Wright4TheJob/PiKwonDo/Block Diagram/Block Diagram/Judge Logic.png

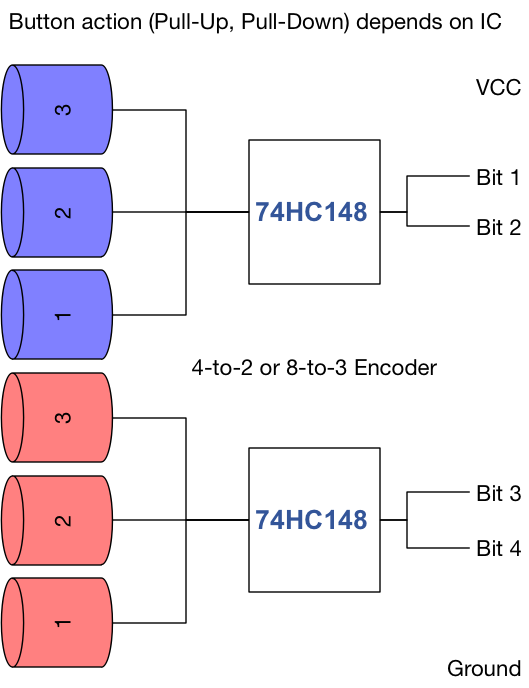
Block Diagram/Block Diagram/Judge Logic.png
