Wright4TheJob/PiKwonDo/Block Diagram/Block Diagram/Software Flow.png

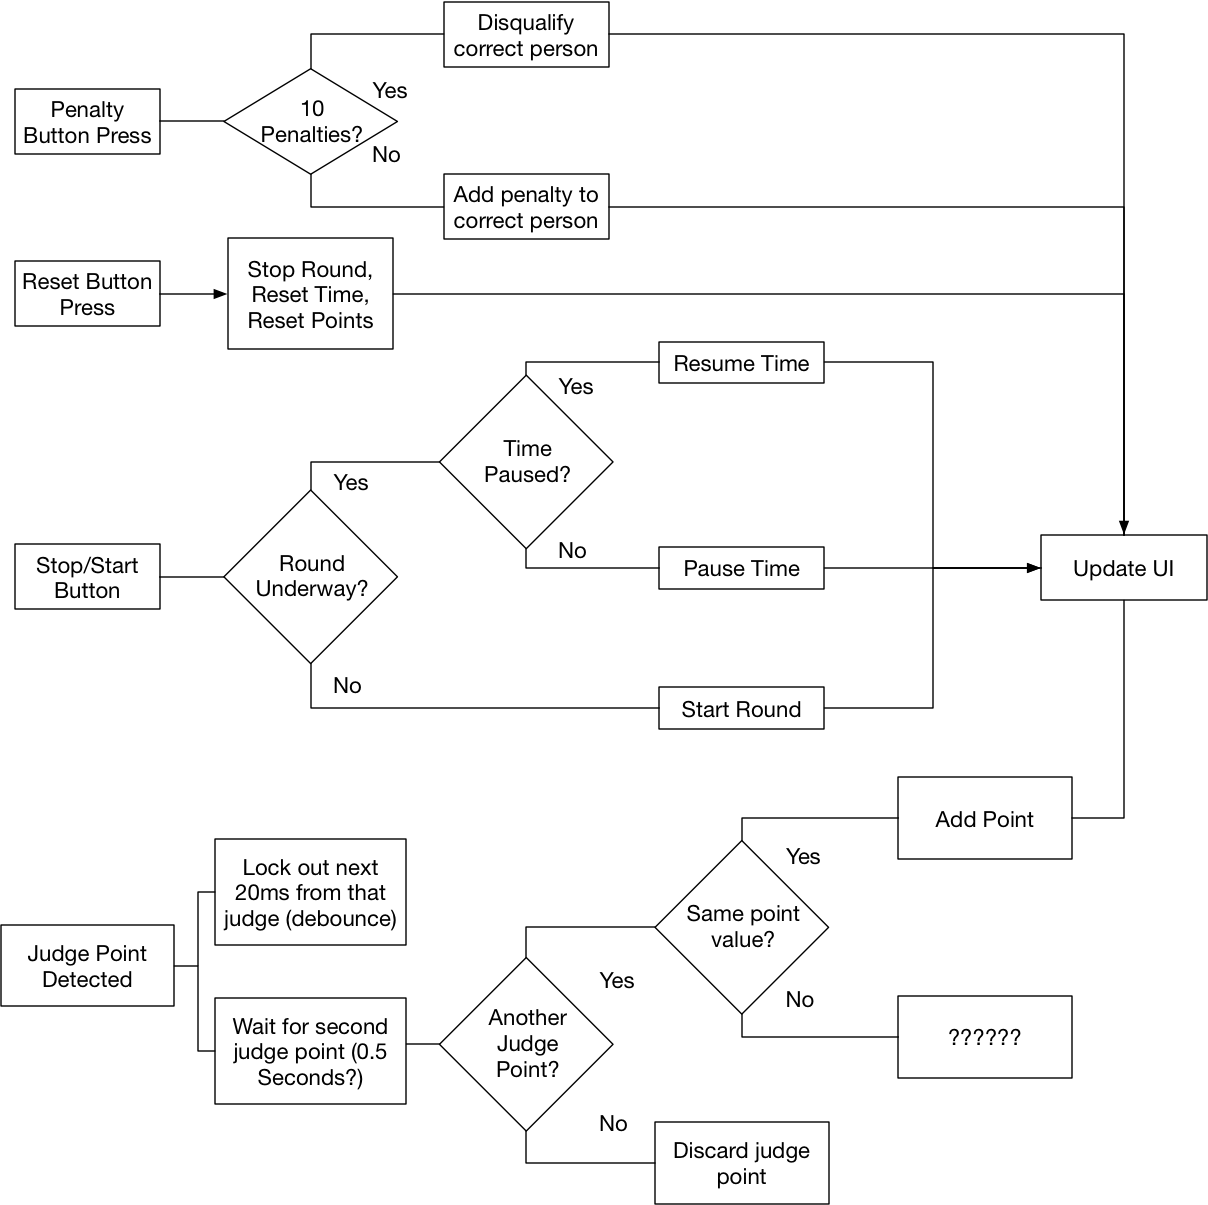
Block Diagram/Block Diagram/Software Flow.png
