Wright4TheJob/PiKwonDo/Block Diagram/Block Diagram/System Diagram.png

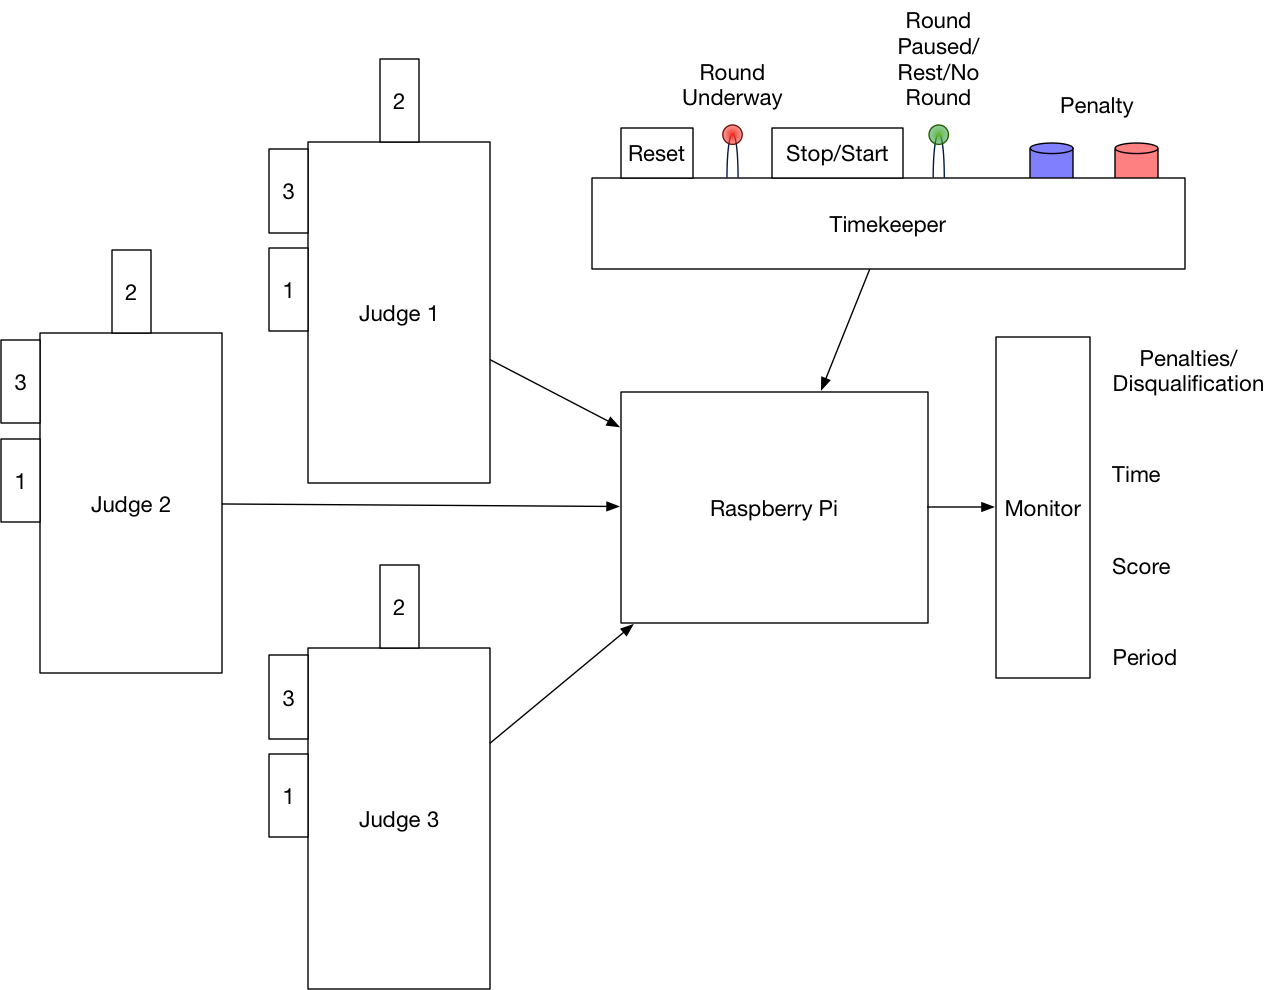
Block Diagram/Block Diagram/System Diagram.png
