Wright4TheJob/PiKwonDo/Hardware/Judge Box/Button Layouts/ButtonGrid.png

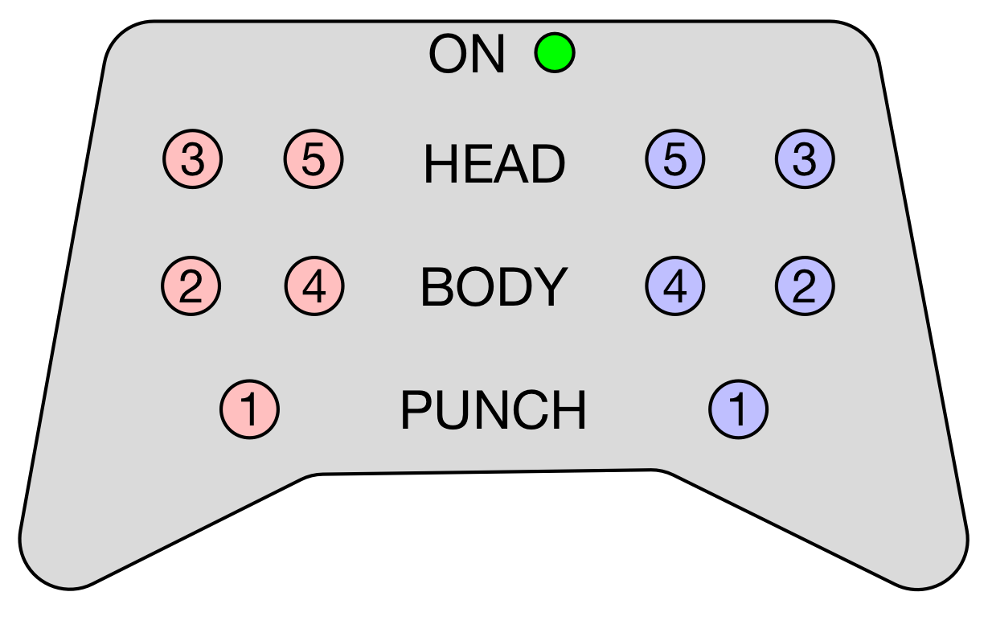
Hardware/Judge Box/Button Layouts/ButtonGrid.png
