Wright4TheJob/PiKwonDo/Hardware/Judge Box/Button Layouts/ButtonLine.png

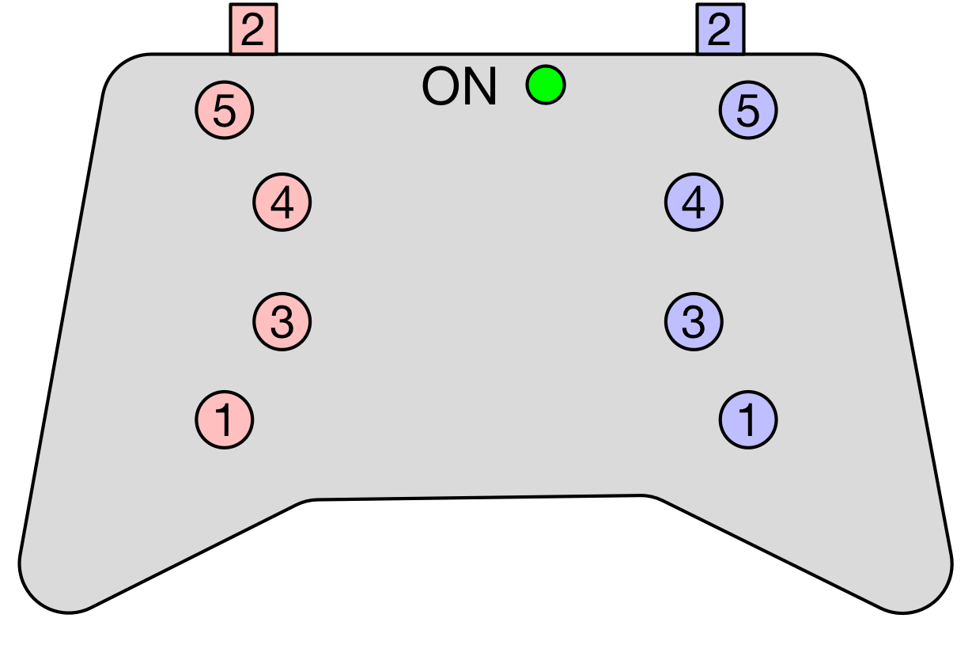
Hardware/Judge Box/Button Layouts/ButtonLine.png
