Wright4TheJob/PiKwonDo/Hardware/Main Box/Raspberry Pi Zero/32,768 Khz Crystal.SLDPRT

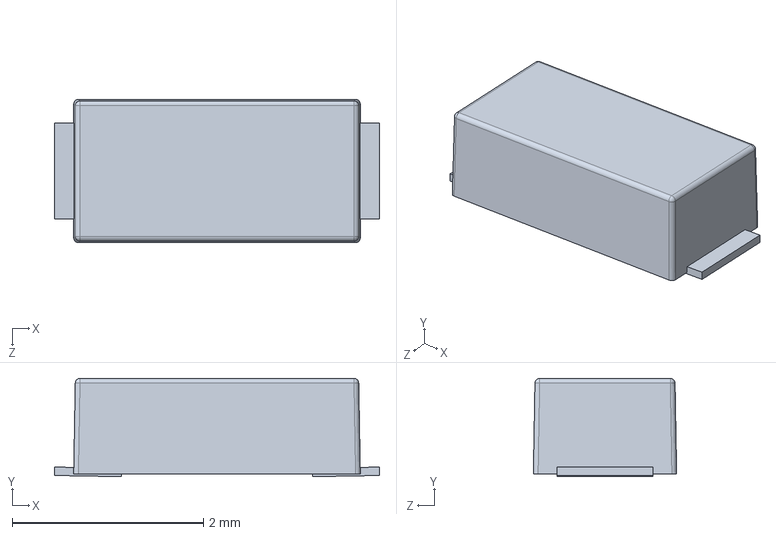
[picture p21: CAD file, 2020-05-05]
Hardware/Main Box/Raspberry Pi Zero/32,768 Khz Crystal.SLDPRT
3.40 x 1.03 x 1.50 mm
