Wright4TheJob/PiKwonDo/Hardware/Common Components/TriggerButton.SLDPRT

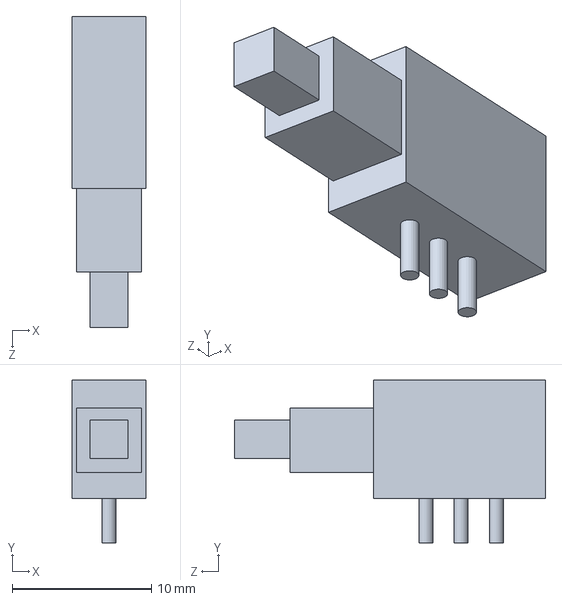
[picture p22: CAD file, 2020-07-26]
Hardware/Common Components/TriggerButton.SLDPRT
5.35 x 11.7 x 22.4 mm
