Wright4TheJob/PiKwonDo/Hardware/Judge Box/JudgeEnclosureBackSolid.3MF

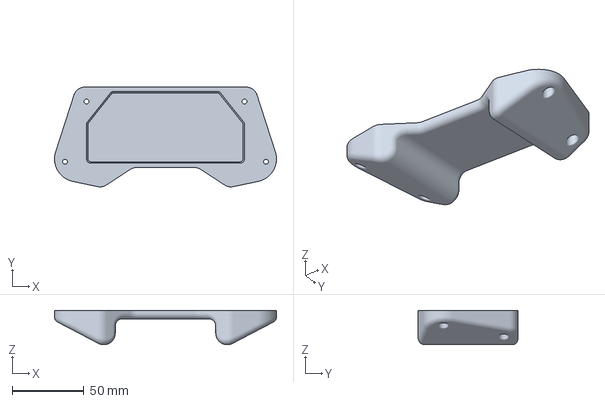
[picture p23: CAD file, 2020-08-09]
Hardware/Judge Box/JudgeEnclosureBackSolid.3MF
154.6 x 69.5 x 24.0 mm
