Wright4TheJob/PiKwonDo/Hardware/Main Box/Raspberry Pi Zero/hdmi type C.SLDPRT

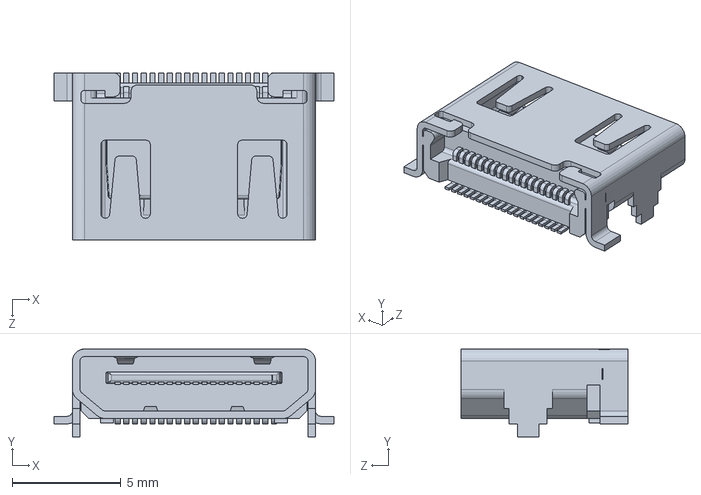
[picture p24: CAD file, 2020-05-05]
Hardware/Main Box/Raspberry Pi Zero/hdmi type C.SLDPRT
12.9 x 4.05 x 7.70 mm
