Wright4TheJob/PiKwonDo/Hardware/Timer Box/TimerPCB.SLDPRT

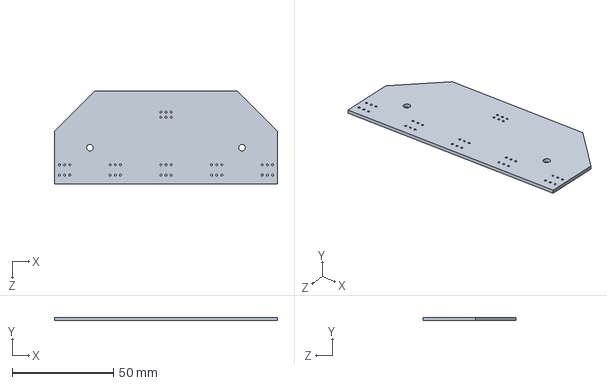
[picture p25: CAD file, 2020-07-26]
Hardware/Timer Box/TimerPCB.SLDPRT
110.0 x 1.53 x 46.0 mm
