Wright4TheJob/PiKwonDo/Hardware/Common Components/TopButtonCoverPlain.SLDPRT

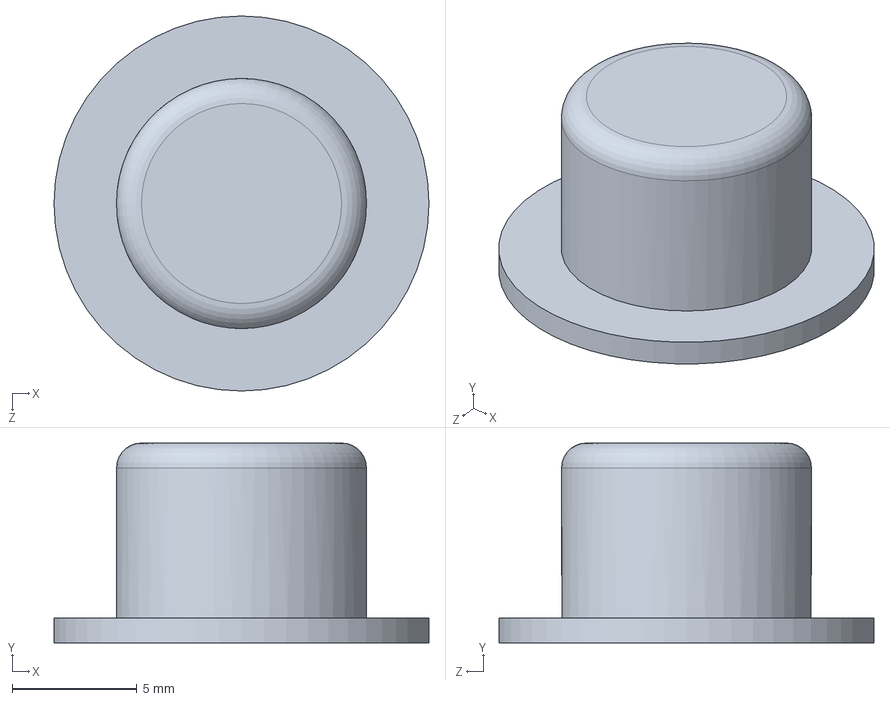
[picture p26: CAD file, 2020-07-26]
Hardware/Common Components/TopButtonCoverPlain.SLDPRT
15.0 x 8.00 x 15.0 mm
