Wright4TheJob/PiKwonDo/Hardware/Judge Box/JudgeEnclosureBack.SLDPRT

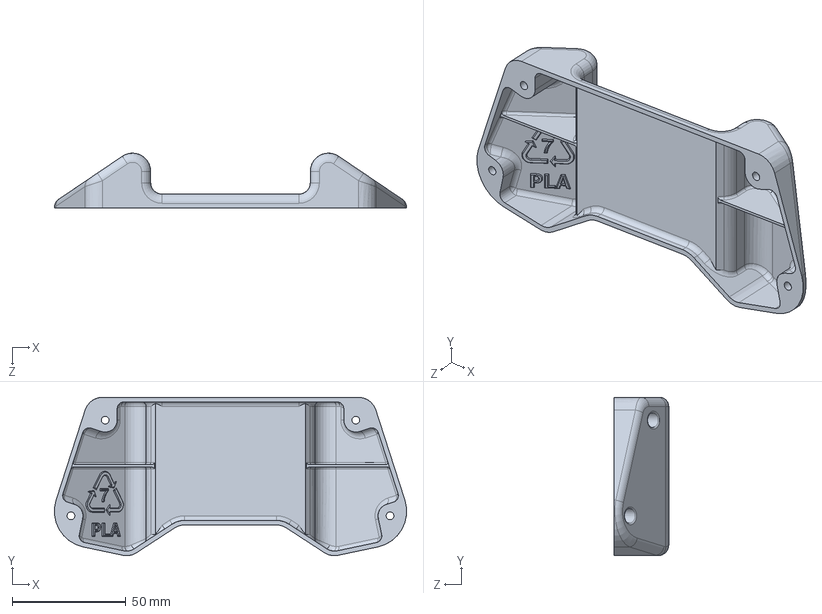
[picture p27: CAD file, 2020-08-09]
Hardware/Judge Box/JudgeEnclosureBack.SLDPRT
154.5 x 69.5 x 24.0 mm
