Wright4TheJob/PiKwonDo/Hardware/Main Box/Raspberry Pi Zero/Raspberry_pizero_PCB.SLDPRT

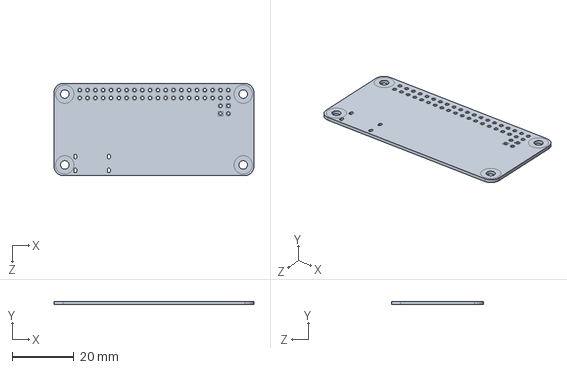
[picture p28: CAD file, 2020-05-05]
Hardware/Main Box/Raspberry Pi Zero/Raspberry_pizero_PCB.SLDPRT
65.0 x 1.00 x 30.0 mm
