Wright4TheJob/PiKwonDo/Hardware/Common Components/PushButton.SLDPRT

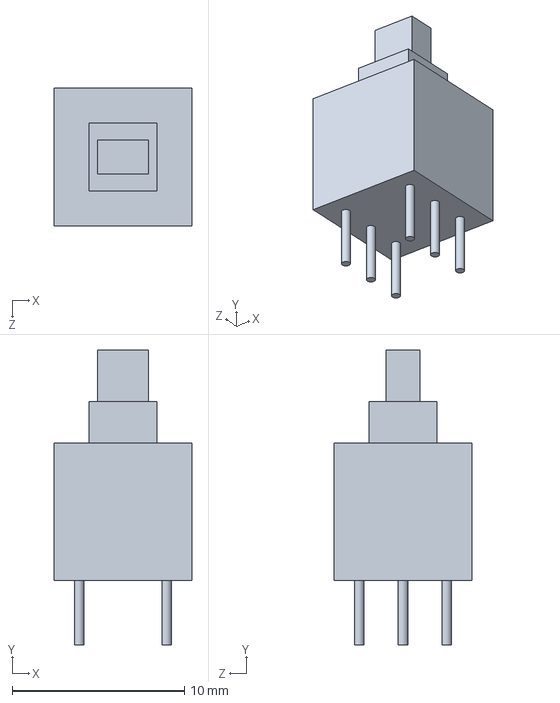
[picture p29: CAD file, 2020-07-26]
Hardware/Common Components/PushButton.SLDPRT
8.00 x 17.1 x 8.00 mm
