Wright4TheJob/PiKwonDo/Hardware/Judge Box/JudgeEnclosureFront.SLDPRT

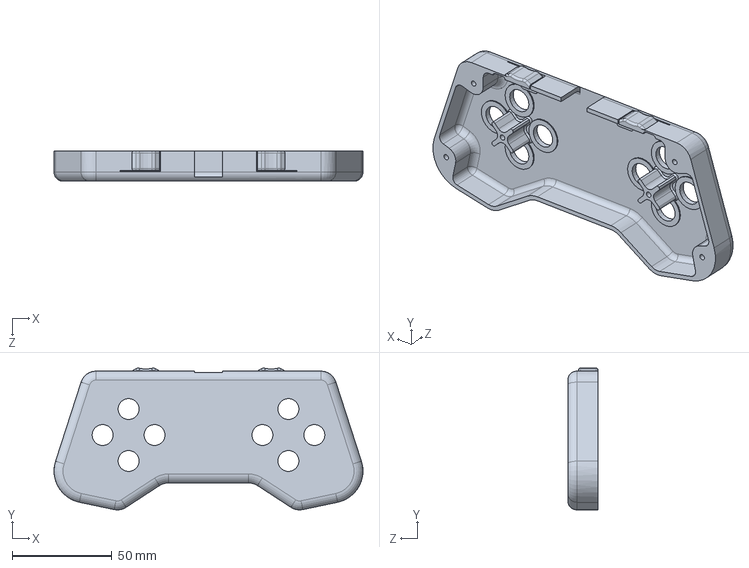
[picture p30: CAD file, 2020-08-09]
Hardware/Judge Box/JudgeEnclosureFront.SLDPRT
154.6 x 71.0 x 15.2 mm
