Wright4TheJob/PiKwonDo/Hardware/Main Box/Raspberry Pi Zero/0805- Capacitor.SLDPRT

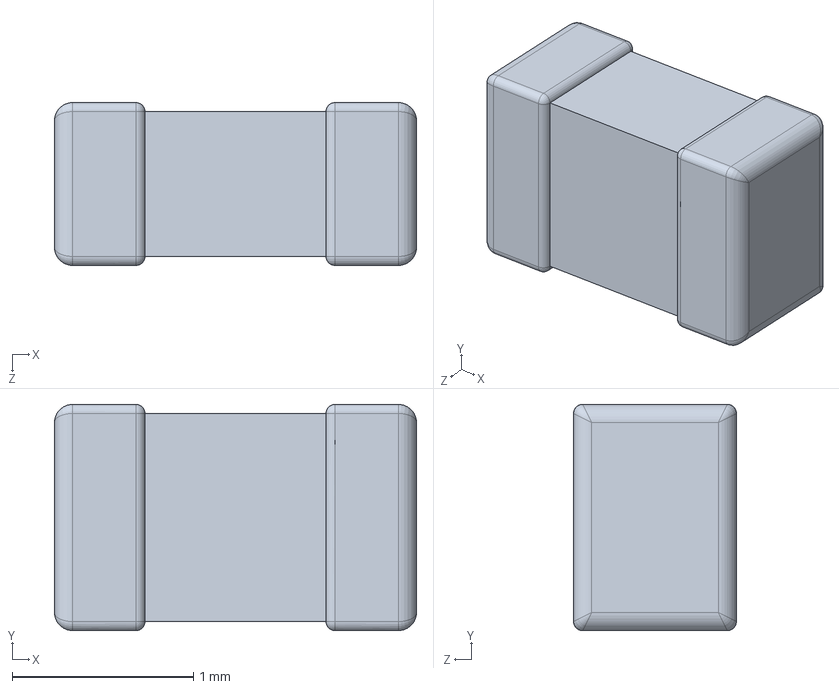
[picture p31: CAD file, 2020-05-05]
Hardware/Main Box/Raspberry Pi Zero/0805- Capacitor.SLDPRT
2.00 x 1.25 x 0.9 mm
