Wright4TheJob/PiKwonDo/Hardware/Timer Box/TimerBoxCaseBottom.SLDPRT

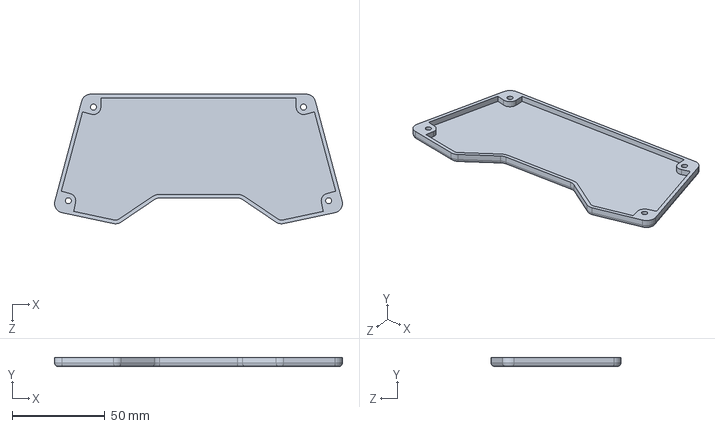
[picture p32: CAD file, 2020-07-26]
Hardware/Timer Box/TimerBoxCaseBottom.SLDPRT
155.3 x 5.00 x 69.9 mm
