Wright4TheJob/PiKwonDo/Hardware/Judge Box/JudgePCB.SLDPRT

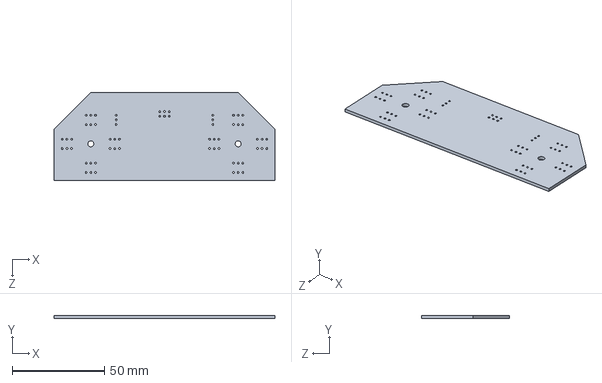
[picture p33: CAD file, 2020-07-26]
Hardware/Judge Box/JudgePCB.SLDPRT
120.0 x 1.53 x 48.0 mm
