Wright4TheJob/PiKwonDo/Hardware/Main Box/PinHeader.SLDPRT

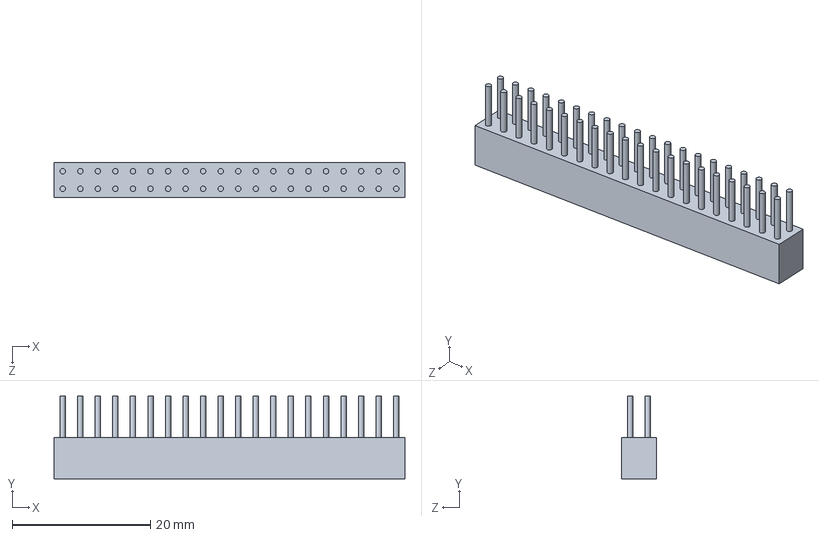
[picture p34: CAD file, 2020-05-05]
Hardware/Main Box/PinHeader.SLDPRT
50.8 x 12.0 x 5.08 mm
