Wright4TheJob/PiKwonDo/Hardware/Main Box/Raspberry Pi Zero/0204 - Capacitor.SLDPRT

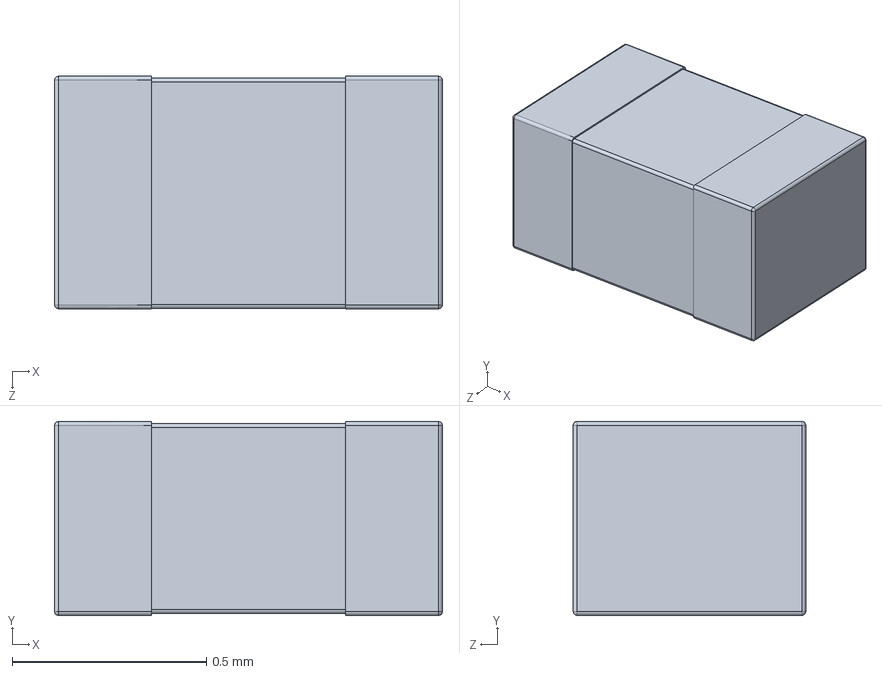
[picture p35: CAD file, 2020-05-05]
Hardware/Main Box/Raspberry Pi Zero/0204 - Capacitor.SLDPRT
1.00 x 0.5 x 0.6 mm
