Wright4TheJob/PiKwonDo/Hardware/Timer Box/TimerBoxCaseTop.SLDPRT

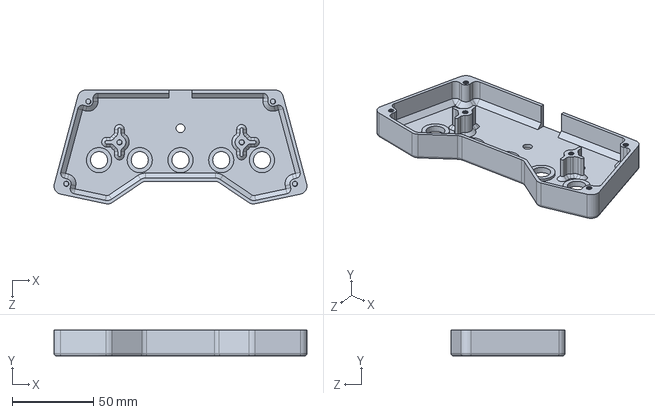
[picture p36: CAD file, 2020-07-26]
Hardware/Timer Box/TimerBoxCaseTop.SLDPRT
155.3 x 15.9 x 69.9 mm
