Wright4TheJob/PiKwonDo/Hardware/Main Box/HAT-PCB.SLDPRT

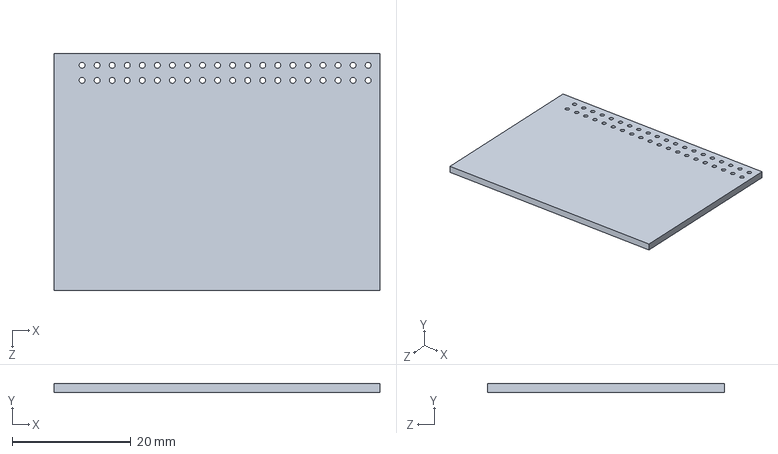
[picture p37: CAD file, 2020-05-05]
Hardware/Main Box/HAT-PCB.SLDPRT
55.0 x 1.50 x 40.0 mm
