Wright4TheJob/PiKwonDo/Hardware/Main Box/Raspberry Pi Zero/1210 inductor.SLDPRT

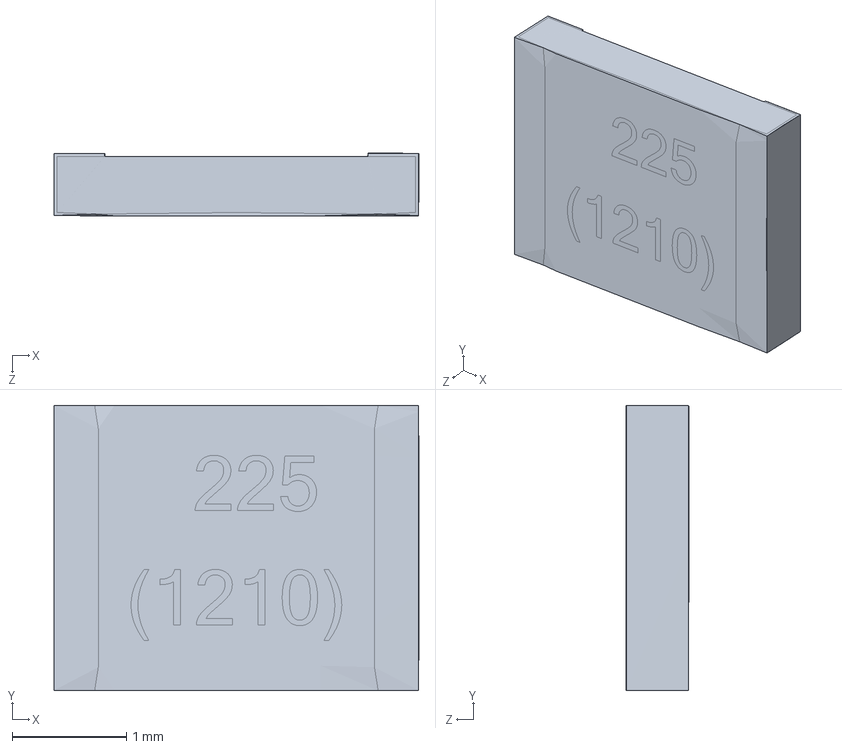
[picture p38: CAD file, 2020-05-05]
Hardware/Main Box/Raspberry Pi Zero/1210 inductor.SLDPRT
3.20 x 2.50 x 0.55 mm
