Wright4TheJob/PiKwonDo/Hardware/Common Components/RJ12Socket.SLDPRT

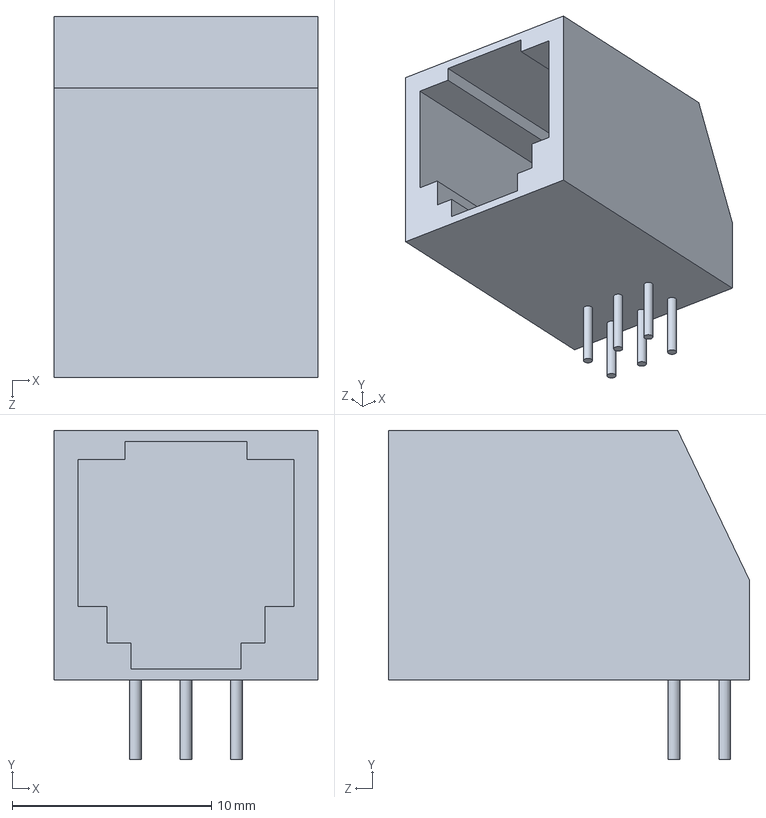
[picture p39: CAD file, 2020-07-26]
Hardware/Common Components/RJ12Socket.SLDPRT
13.2 x 16.5 x 18.1 mm
