Wright4TheJob/PiKwonDo/Hardware/Main Box/Raspberry Pi Zero/6-Pin SOT.SLDPRT

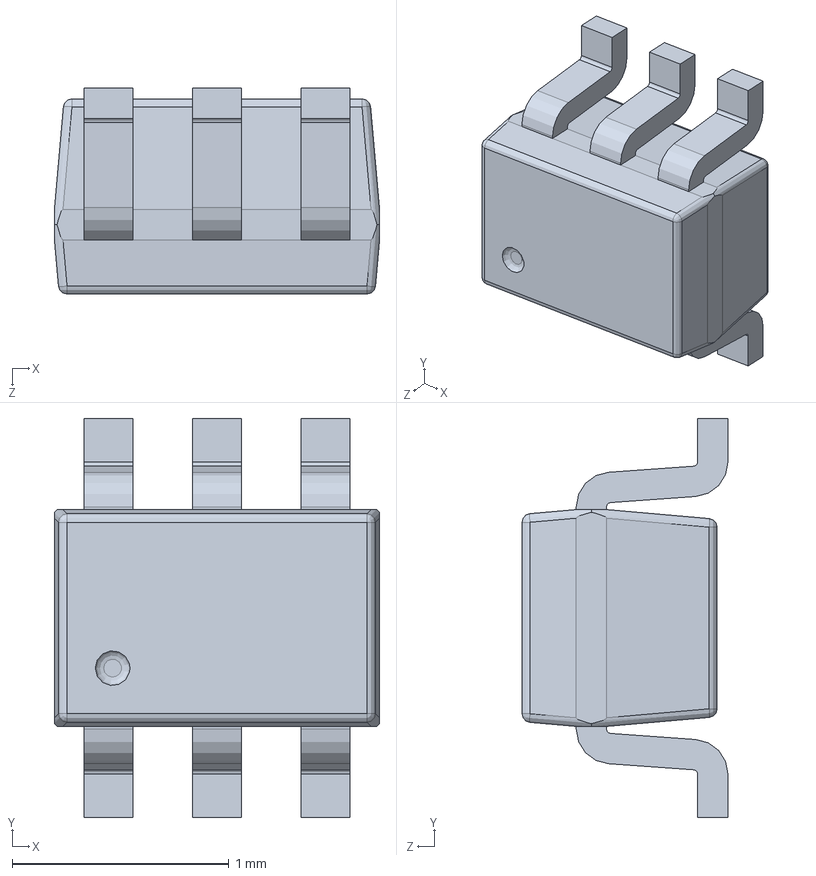
[picture p40: CAD file, 2020-05-05]
Hardware/Main Box/Raspberry Pi Zero/6-Pin SOT.SLDPRT
1.50 x 1.84 x 0.95 mm
