Wright4TheJob/PiKwonDo/Hardware/Main Box/Raspberry Pi Zero/CAP-0306.SLDPRT

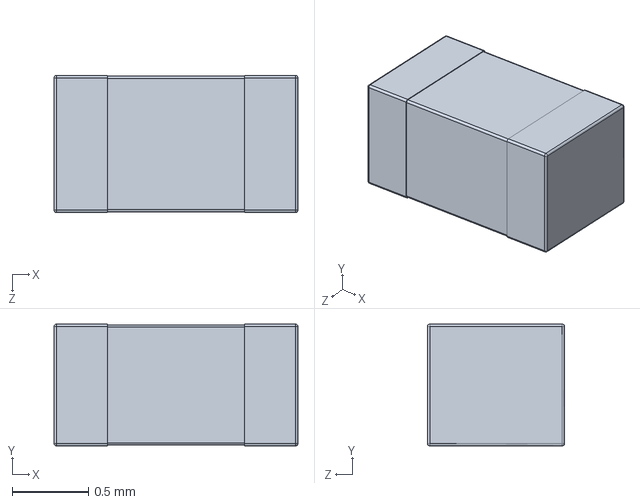
[picture p41: CAD file, 2020-05-05]
Hardware/Main Box/Raspberry Pi Zero/CAP-0306.SLDPRT
1.60 x 0.8 x 0.9 mm
