Wright4TheJob/PiKwonDo/Hardware/Common Components/RaspberryPi3B+.SLDPRT

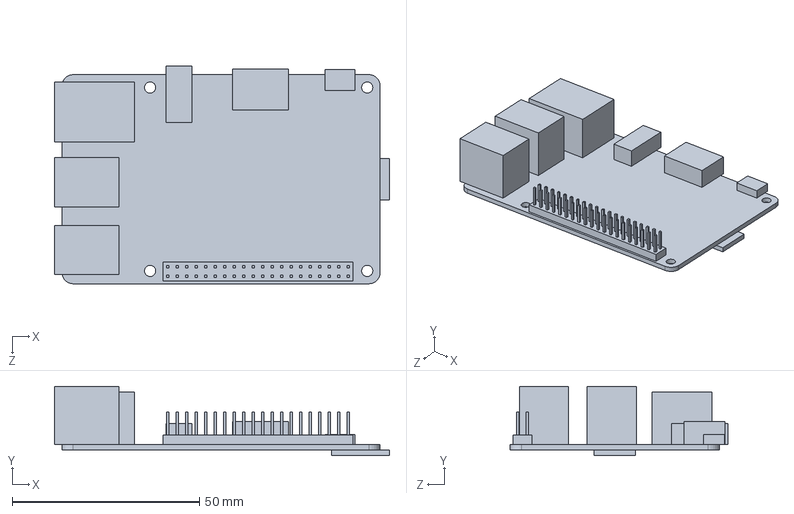
[picture p42: CAD file, 2020-05-05]
Hardware/Common Components/RaspberryPi3B+.SLDPRT
89.5 x 18.5 x 58.2 mm
