Wright4TheJob/PiKwonDo/Hardware/Main Box/Raspberry Pi Zero/micro sd molex.SLDPRT

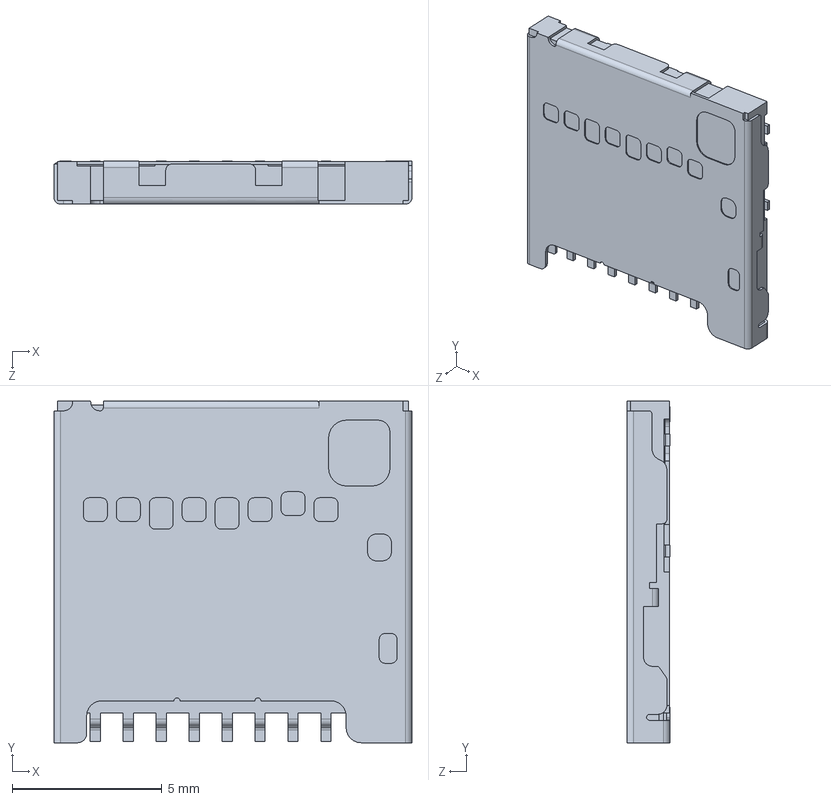
[picture p43: CAD file, 2020-05-05]
Hardware/Main Box/Raspberry Pi Zero/micro sd molex.SLDPRT
12.0 x 11.4 x 1.45 mm
