Wright4TheJob/PiKwonDo/Hardware/Main Box/Raspberry Pi Zero/Raspberry_pizero_BCM2835 with VC4.SLDPRT

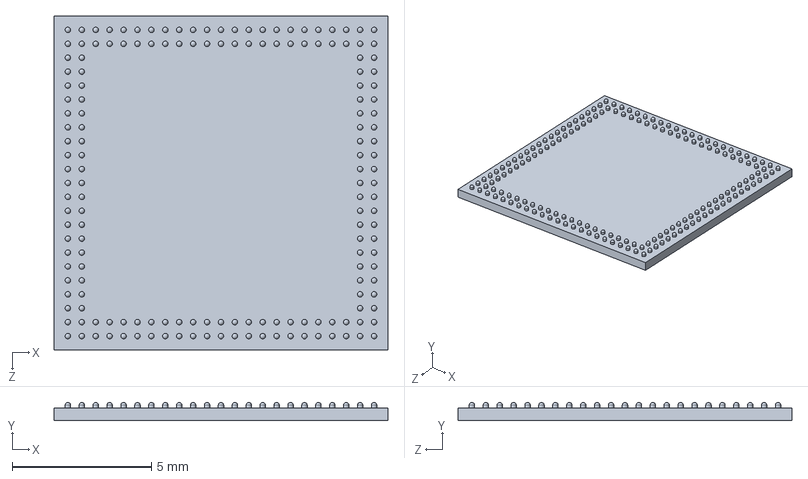
[picture p44: CAD file, 2020-05-05]
Hardware/Main Box/Raspberry Pi Zero/Raspberry_pizero_BCM2835 with VC4.SLDPRT
12.0 x 0.65 x 12.0 mm
