Wright4TheJob/PiKwonDo/Hardware/Common Components/Dip8Socket.SLDPRT

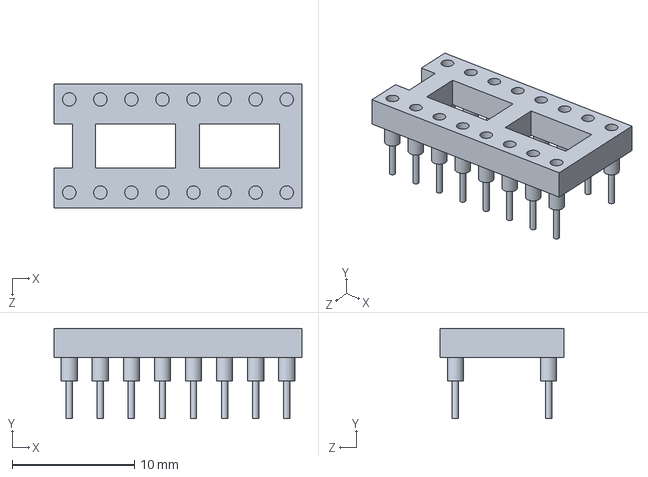
[picture p45: CAD file, 2018-04-19]
Hardware/Common Components/Dip8Socket.SLDPRT
20.3 x 7.38 x 10.1 mm
