Wright4TheJob/PiKwonDo/Hardware/Main Box/Raspberry Pi Zero/Voltage Regulator 3x3mm 12-Pin.SLDPRT

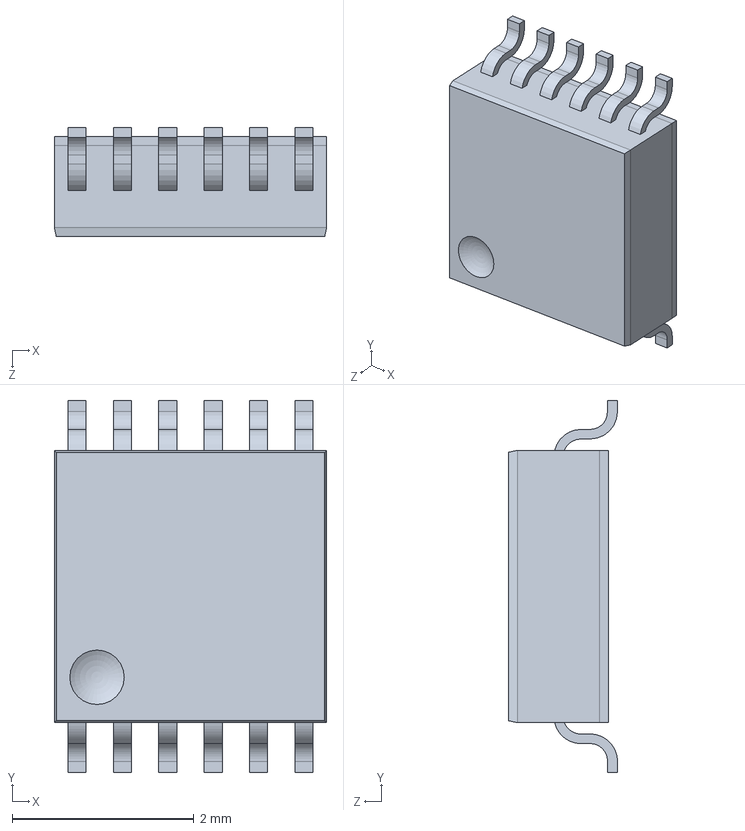
[picture p46: CAD file, 2020-05-05]
Hardware/Main Box/Raspberry Pi Zero/Voltage Regulator 3x3mm 12-Pin.SLDPRT
3.00 x 4.10 x 1.20 mm
