Wright4TheJob/PiKwonDo/Hardware/Main Box/Raspberry Pi Zero/0204- Resistor.SLDPRT

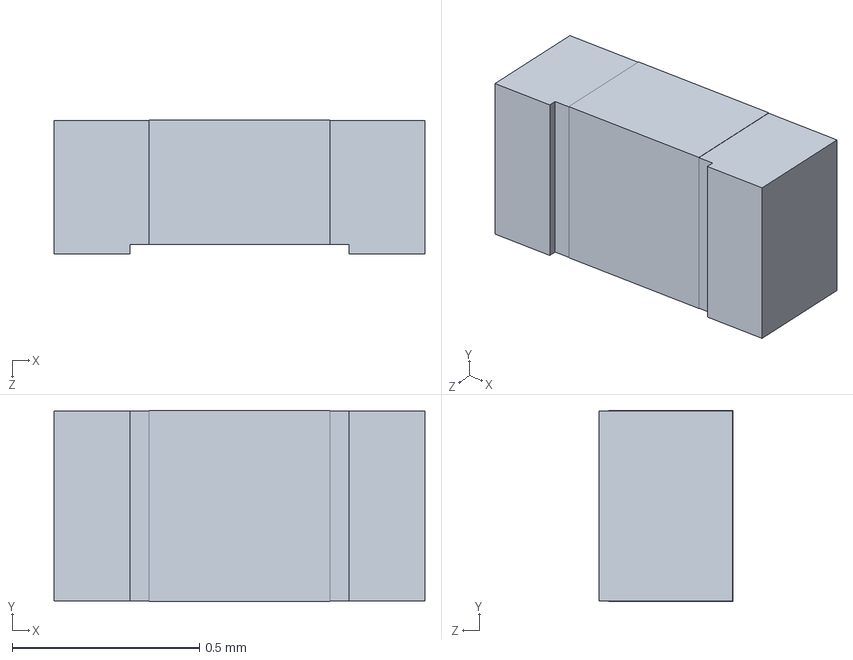
[picture p47: CAD file, 2020-05-05]
Hardware/Main Box/Raspberry Pi Zero/0204- Resistor.SLDPRT
0.991 x 0.51 x 0.357 mm
