Wright4TheJob/PiKwonDo/Hardware/Main Box/Raspberry Pi Zero/Crystal 3.4x2.4mm.SLDPRT

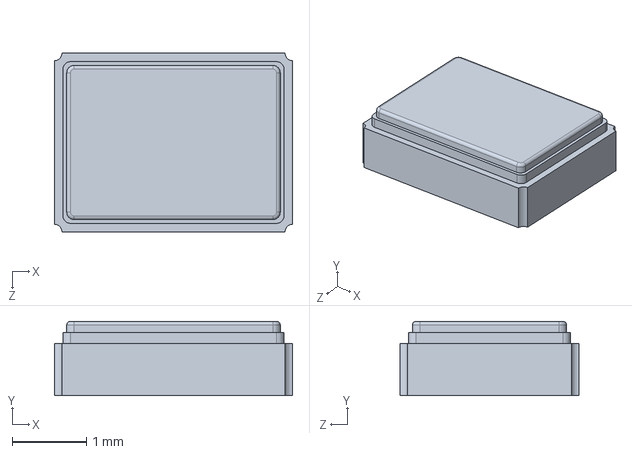
[picture p48: CAD file, 2020-05-05]
Hardware/Main Box/Raspberry Pi Zero/Crystal 3.4x2.4mm.SLDPRT
3.20 x 1.00 x 2.40 mm
