Wright4TheJob/PiKwonDo/Hardware/Main Box/Raspberry Pi Zero/Micro USB_input_female (short)-SMT.SLDPRT

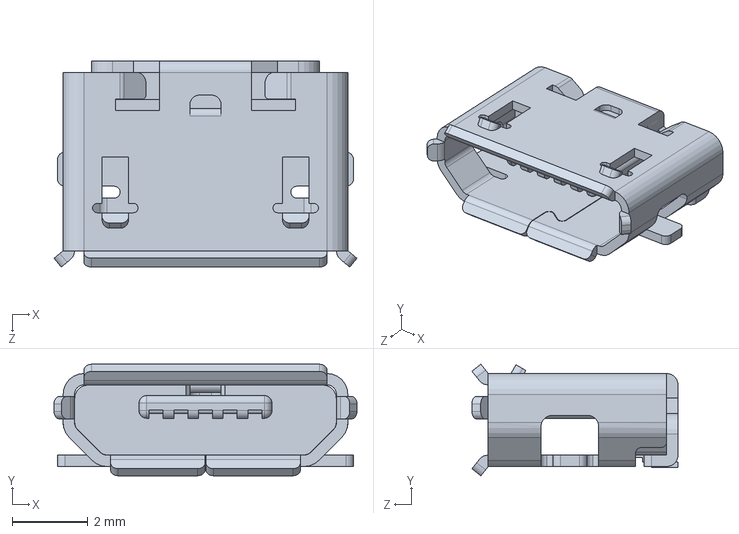
[picture p49: CAD file, 2020-05-05]
Hardware/Main Box/Raspberry Pi Zero/Micro USB_input_female (short)-SMT.SLDPRT
7.98 x 2.94 x 5.43 mm
