Wright4TheJob/PiKwonDo/Software/PiKwonDo/unit_test.py

"""Unit and integration tests for PiKwonDo."""

import time
import threading
import math

import unittest
from PiKwonDo import PiKwonDo
from utilities import UnknownFighterError
import pkdtimer
import gui
# from PyQt5.QtWidgets import QApplication
# import sys
# class KnownValues(unittest.TestCase):
# self.fighterValues = ((0,1),(1,4))

# def test_square_known_values(self):
# '''Square Integers should return known values with known inputs'''
# for integer, knownValue in self.fighterValues:
# result = PiKwonDo.MainWindow.penaltyDetected(integer)
# self.assertEqual(knownValue,result)

# def test_parabola_results(self):
# '''parabola should return known results'''
# result = MainProgram.valueOfParabola([0,0,0],1)
# self.assertEqual(0,result)


class FrontEndController(unittest.TestCase):
    """Test that all GUI functions can be run without error."""

    def test_frontendcontroller_init(self):
        """Create the front end controller class without error."""
        pkd = PiKwonDo()
        try:
            gui.FrontEndController(pkd)
        except:
            self.fail("FrontEndController raised exception unexpectedly!")


# class CanCreateGUI(unittest.TestCase):
#    """Test that all GUI functions can be run without error."""
#
#    def test_mainwindow_init(self):
#        """Create the main window class without error."""
#        pkd = PiKwonDo(create_gui=False)
#        try:
#            gui.MainWindow(pkd)
#        except:
#            self.fail("gui.MainWindow() raised exception unexpectedly!")
#
#    def test_setup_ui(self):
#        """Test the setup_ui function."""
#        pkd = PiKwonDo(create_gui=False)
#        main_window = gui.MainWindow(pkd)
#        try:
#            main_window.setup_ui(main_window)
#        except:
#            self.fail("main_window.setup_ui() raised exception unexpectedly!")


class BadInput(unittest.TestCase):
    """Test error handling of functions."""

    bad_fighter_values = (-1, 2, 10)

    def test_unknown_fighter_code_penalty(self):
        """Penalty function should fail with bad fighter input."""
        for bad_value in self.bad_fighter_values:
            main = PiKwonDo(create_gui=False)
            with self.assertRaises(UnknownFighterError):
                main.penalty_detected(bad_value)

    def test_unknown_fighter_code_point(self):
        """Point function should fail with invalid fighter input."""
        for bad_value in self.bad_fighter_values:
            main = PiKwonDo(create_gui=False)
            with self.assertRaises(UnknownFighterError):
                main.point_detected(bad_value, 1)


class TickingTimer(unittest.TestCase):
    """Test timing functions for accuracy and emissions."""

    def setUp(self):
        """Set up class variables."""
        self.ticks = 0
        self.times = []

    def test_known_duration(self):
        """Set a timer for a known duration."""
        # print('test_known_duration')
        test_timer = pkdtimer.TimerThread(0.1, interval=0.01)
        test_timer.start()

    def test_return_time(self):
        """Request current time from the running timer."""
        # print('test_return_time')
        time_before = time.monotonic()
        test_timer = pkdtimer.TimerThread(0.1, interval=0.01)

        def on_tick():
            runtime = test_timer.current_time()
            time_after = time.monotonic()
            self.assertLessEqual(runtime, time_after-time_before)
        test_timer.tick = on_tick
        test_timer.start()
        test_timer.wait_until_done()

    def test_calls_done(self):
        """Ensure the timer finishes with correct signal."""
        # print('test_calls_done')
        is_done = threading.Event()
        timer = pkdtimer.TimerThread(0.1, interval=0.01)

        def on_tick():
            self.assertFalse(is_done.is_set())

        def on_done():
            is_done.set()
        timer.tick = on_tick
        timer.done = on_done
        timer.start()
        timer.wait_until_done()
        self.assertTrue(is_done.wait(timeout=1))

    def test_number_of_ticks(self):
        """Ensure number of ticks is correct for given duration."""
        duration = 0.1
        interval = 0.01
        ticks_max = math.floor(duration/interval)
        ticks_min = ticks_max - 2
        timer = pkdtimer.TimerThread(duration, interval=interval)
        self.ticks = 0

        def on_tick():
            self.ticks += 1
        timer.tick = on_tick
        timer.start()
        timer.wait_until_done()
        self.assertLessEqual(self.ticks, ticks_max)
        self.assertGreaterEqual(self.ticks, ticks_min)

    def test_time_between_ticks(self):
        """Ensure that spacing between ticks is correct and consistant."""
        duration = 0.1
        interval = 0.01
        max_deviation = 0.5*interval  # 50% error allowed
        timer = pkdtimer.TimerThread(duration, interval=interval)
        self.times = []

        def on_tick():
            self.times.append(timer.current_time())
        timer.tick = on_tick
        timer.start()
        timer.wait_until_done()
        time_deltas = []
        for i in range(0, len(self.times)-1):
            time_deltas.append(self.times[i+1]-self.times[i])
        self.assertGreaterEqual(interval+max_deviation, max(time_deltas))
        # other tests:  time between ticks is acceptable


if __name__ == '__main__':
    unittest.main()
